squiggles1024/MouseF4/Core/Inc/mouse_keydefs.h

/*
 * mouse_keydefs.h
 *
 *  Created on: Oct 18, 2021
 *      Author: evanl
 */

#ifndef INC_MOUSE_KEYDEFS_H_
#define INC_MOUSE_KEYDEFS_H_

//modifier key masks
#define KEY_MOD_LCTRL  0x01
#define KEY_MOD_LSHIFT 0x02
#define KEY_MOD_LALT   0x04
#define KEY_MOD_LMETA  0x08
#define KEY_MOD_RCTRL  0x10
#define KEY_MOD_RSHIFT 0x20
#define KEY_MOD_RALT   0x40
#define KEY_MOD_RMETA  0x80

//mouse button masks
#define MOUSE_BTN_LEFT_Msk 0x01
#define MOUSE_BTN_RIGHT_Msk 0x02
#define MOUSE_BTN_3_Msk 0x04
#define MOUSE_BTN_4_Msk 0x08
#define MOUSE_BTN_5_Msk 0x10

/**
 * Scan codes - last N slots in the HID report (usually 6).
 * 0x00 if no key pressed.
 *
 * If more than N keys are pressed, the HID reports
 * KEY_ERR_OVF in all slots to indicate this condition.
 */

#define KEY_NONE 0x00 // No key pressed
#define KEY_ERR_OVF 0x01 //  Keyboard Error Roll Over - used for all slots if too many keys are pressed ("Phantom key")
// 0x02 //  Keyboard POST Fail
// 0x03 //  Keyboard Error Undefined
#define KEY_A 0x04 // Keyboard a and A
#define KEY_B 0x05 // Keyboard b and B
#define KEY_C 0x06 // Keyboard c and C
#define KEY_D 0x07 // Keyboard d and D
#define KEY_E 0x08 // Keyboard e and E
#define KEY_F 0x09 // Keyboard f and F
#define KEY_G 0x0a // Keyboard g and G
#define KEY_H 0x0b // Keyboard h and H
#define KEY_I 0x0c // Keyboard i and I
#define KEY_J 0x0d // Keyboard j and J
#define KEY_K 0x0e // Keyboard k and K
#define KEY_L 0x0f // Keyboard l and L
#define KEY_M 0x10 // Keyboard m and M
#define KEY_N 0x11 // Keyboard n and N
#define KEY_O 0x12 // Keyboard o and O
#define KEY_P 0x13 // Keyboard p and P
#define KEY_Q 0x14 // Keyboard q and Q
#define KEY_R 0x15 // Keyboard r and R
#define KEY_S 0x16 // Keyboard s and S
#define KEY_T 0x17 // Keyboard t and T
#define KEY_U 0x18 // Keyboard u and U
#define KEY_V 0x19 // Keyboard v and V
#define KEY_W 0x1a // Keyboard w and W
#define KEY_X 0x1b // Keyboard x and X
#define KEY_Y 0x1c // Keyboard y and Y
#define KEY_Z 0x1d // Keyboard z and Z

#define KEY_1 0x1e // Keyboard 1 and !
#define KEY_2 0x1f // Keyboard 2 and @
#define KEY_3 0x20 // Keyboard 3 and #
#define KEY_4 0x21 // Keyboard 4 and $
#define KEY_5 0x22 // Keyboard 5 and %
#define KEY_6 0x23 // Keyboard 6 and ^
#define KEY_7 0x24 // Keyboard 7 and &
#define KEY_8 0x25 // Keyboard 8 and *
#define KEY_9 0x26 // Keyboard 9 and (
#define KEY_0 0x27 // Keyboard 0 and )

#define KEY_ENTER 0x28 // Keyboard Return (ENTER)
#define KEY_ESC 0x29 // Keyboard ESCAPE
#define KEY_BACKSPACE 0x2a // Keyboard DELETE (Backspace)
#define KEY_TAB 0x2b // Keyboard Tab
#define KEY_SPACE 0x2c // Keyboard Spacebar
#define KEY_MINUS 0x2d // Keyboard - and _
#define KEY_EQUAL 0x2e // Keyboard = and +
#define KEY_LEFTBRACE 0x2f // Keyboard [ and {
#define KEY_RIGHTBRACE 0x30 // Keyboard ] and }
#define KEY_BACKSLASH 0x31 // Keyboard \ and |
#define KEY_HASHTILDE 0x32 // Keyboard Non-US # and ~
#define KEY_SEMICOLON 0x33 // Keyboard ; and :
#define KEY_APOSTROPHE 0x34 // Keyboard ' and "
#define KEY_GRAVE 0x35 // Keyboard ` and ~
#define KEY_COMMA 0x36 // Keyboard , and <
#define KEY_DOT 0x37 // Keyboard . and >
#define KEY_SLASH 0x38 // Keyboard / and ?
#define KEY_CAPSLOCK 0x39 // Keyboard Caps Lock

#define KEY_F1 0x3a // Keyboard F1
#define KEY_F2 0x3b // Keyboard F2
#define KEY_F3 0x3c // Keyboard F3
#define KEY_F4 0x3d // Keyboard F4
#define KEY_F5 0x3e // Keyboard F5
#define KEY_F6 0x3f // Keyboard F6
#define KEY_F7 0x40 // Keyboard F7
#define KEY_F8 0x41 // Keyboard F8
#define KEY_F9 0x42 // Keyboard F9
#define KEY_F10 0x43 // Keyboard F10
#define KEY_F11 0x44 // Keyboard F11
#define KEY_F12 0x45 // Keyboard F12

#define KEY_SYSRQ 0x46 // Keyboard Print Screen
#define KEY_SCROLLLOCK 0x47 // Keyboard Scroll Lock
#define KEY_PAUSE 0x48 // Keyboard Pause
#define KEY_INSERT 0x49 // Keyboard Insert
#define KEY_HOME 0x4a // Keyboard Home
#define KEY_PAGEUP 0x4b // Keyboard Page Up
#define KEY_DELETE 0x4c // Keyboard Delete Forward
#define KEY_END 0x4d // Keyboard End
#define KEY_PAGEDOWN 0x4e // Keyboard Page Down
#define KEY_RIGHT 0x4f // Keyboard Right Arrow
#define KEY_LEFT 0x50 // Keyboard Left Arrow
#define KEY_DOWN 0x51 // Keyboard Down Arrow
#define KEY_UP 0x52 // Keyboard Up Arrow

#define KEY_NUMLOCK 0x53 // Keyboard Num Lock and Clear
#define KEY_KPSLASH 0x54 // Keypad /
#define KEY_KPASTERISK 0x55 // Keypad *
#define KEY_KPMINUS 0x56 // Keypad -
#define KEY_KPPLUS 0x57 // Keypad +
#define KEY_KPENTER 0x58 // Keypad ENTER
#define KEY_KP1 0x59 // Keypad 1 and End
#define KEY_KP2 0x5a // Keypad 2 and Down Arrow
#define KEY_KP3 0x5b // Keypad 3 and PageDn
#define KEY_KP4 0x5c // Keypad 4 and Left Arrow
#define KEY_KP5 0x5d // Keypad 5
#define KEY_KP6 0x5e // Keypad 6 and Right Arrow
#define KEY_KP7 0x5f // Keyp ad 7 and Home
#define KEY_KP8 0x60 // Keypad 8 and Up Arrow
#define KEY_KP9 0x61 // Keypad 9 and Page Up
#define KEY_KP0 0x62 // Keypad 0 and Insert
#define KEY_KPDOT 0x63 // Keypad . and Delete


//mask leading bits and use LUT
#define KEY_LEFTCTRL 0xe0 // Keyboard Left Control
#define KEY_LEFTSHIFT 0xe1 // Keyboard Left Shift
#define KEY_LEFTALT 0xe2 // Keyboard Left Alt
#define KEY_LEFTMETA 0xe3 // Keyboard Left GUI
#define KEY_RIGHTCTRL 0xe4 // Keyboard Right Control
#define KEY_RIGHTSHIFT 0xe5 // Keyboard Right Shift
#define KEY_RIGHTALT 0xe6 // Keyboard Right Alt
#define KEY_RIGHTMETA 0xe7 // Keyboard Right GUI
#define MOD_KEY_MSK 0x0F
static const uint16_t MOD_KEY_LUT[] = {KEY_MOD_LCTRL,KEY_MOD_LSHIFT,KEY_MOD_LALT,KEY_MOD_LMETA,KEY_MOD_RCTRL,KEY_MOD_RSHIFT,KEY_MOD_RALT,KEY_MOD_RMETA};


//mask leading bits and use LUT
#define MOUSE_LEFT 0xf0
#define MOUSE_RIGHT 0xf1
#define MOUSE_3 0xf2
#define MOUSE_4 0xf3
#define MOUSE_5 0xf4
#define MOUSE_KEY_MSK 0x0F
static const uint16_t MOUSE_BTN_LUT[]= {MOUSE_BTN_LEFT_Msk,MOUSE_BTN_RIGHT_Msk,MOUSE_BTN_3_Msk,MOUSE_BTN_4_Msk,MOUSE_BTN_5_Msk};

#endif /* INC_MOUSE_KEYDEFS_H_ */
