squiggles1024/MouseF4/Core/Inc/delay_timer.h

/*
 * delay_timer.h
 *
 *  Created on: Oct 19, 2021
 *      Author: evanl
 */

#ifndef INC_DELAY_TIMER_H_
#define INC_DELAY_TIMER_H_
#include "stm32f4xx.h"

void delay_us(uint16_t us);

#endif /* INC_DELAY_TIMER_H_ */
